jdt23/powermeter/powermeterCommon/powerMeter_case_prototypes - 1.png

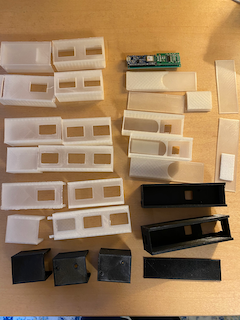
powermeterCommon/powerMeter_case_prototypes - 1.png
