jdt23/powermeter/powermeterSensor/case/powermeterSensor_prototype3_bottom.stl

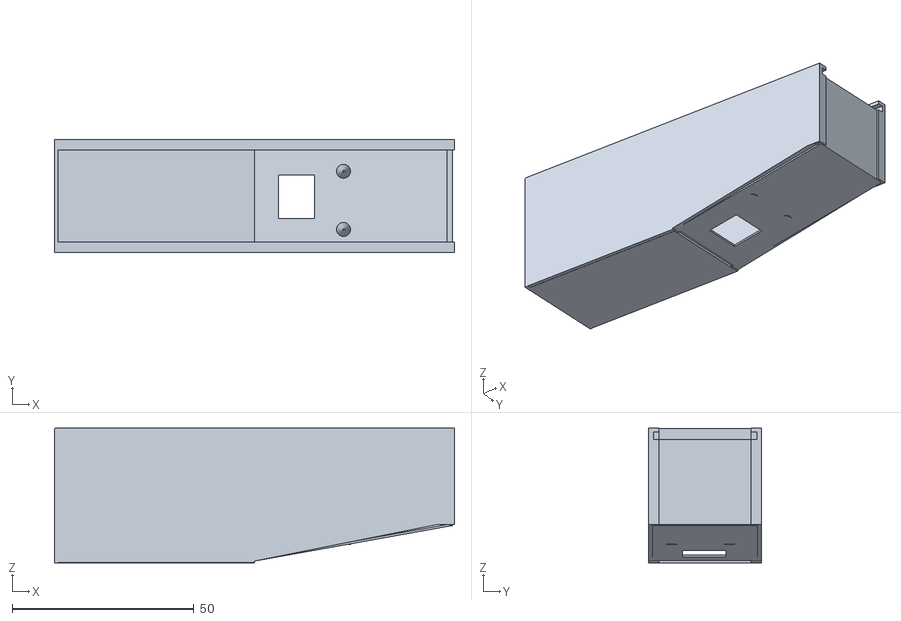
[picture p33: CAD file, 2020-11-20, an earlier design]
powermeterSensor/case/powermeterSensor_prototype3_bottom.stl
110.1 x 31.2 x 37.1
