jdt23/powermeter/powermeterSensor/case/powermeterSensor_prototype3_top.stl

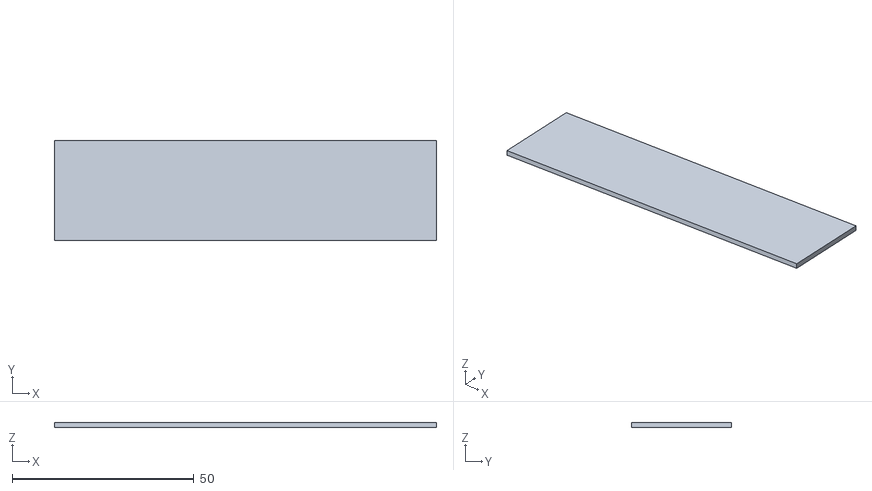
[picture p34: CAD file, 2020-11-20, an earlier design]
powermeterSensor/case/powermeterSensor_prototype3_top.stl
105.0 x 27.5 x 1.50
