jdt23/powermeter/powermeterSensor/case/powermeterSensor_prototype2_bottom.stl

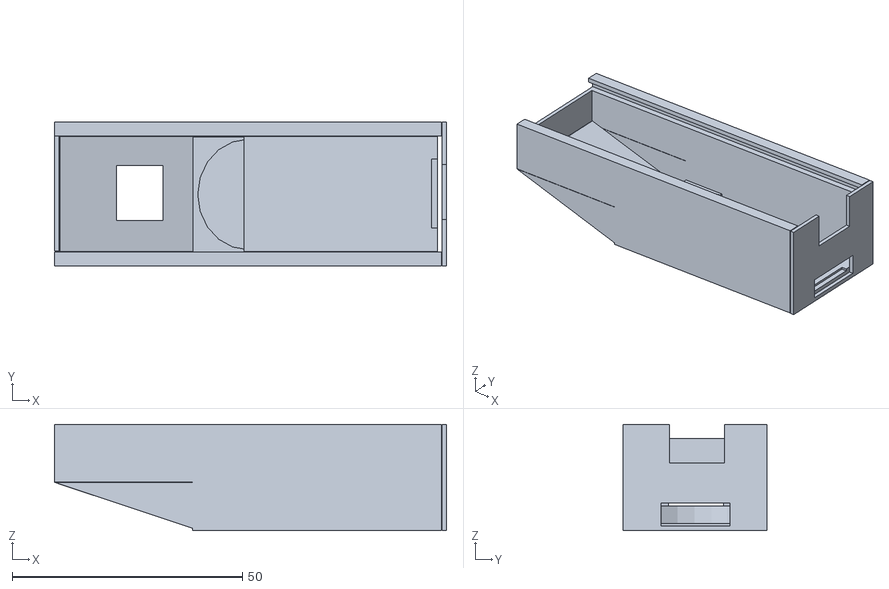
[picture p35: CAD file, 2020-08-12, an earlier design]
powermeterSensor/case/powermeterSensor_prototype2_bottom.stl
85.1 x 31.2 x 23.1
