jdt23/powermeter/powermeterSensor/case/powermeterSensor_prototype1_top.stl

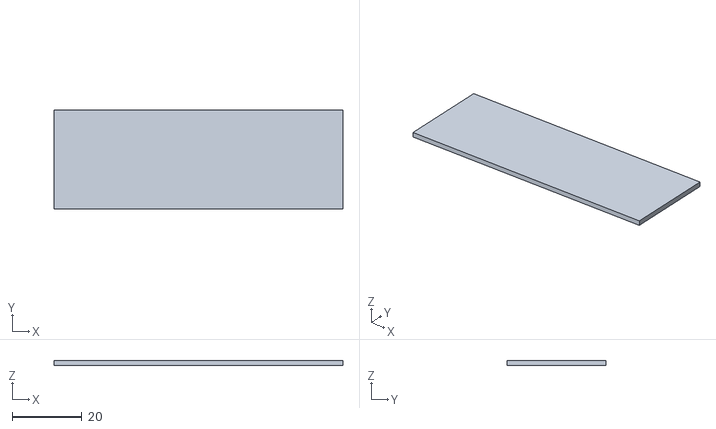
[picture p36: CAD file, 2020-08-12, an earlier design]
powermeterSensor/case/powermeterSensor_prototype1_top.stl
83.0 x 28.5 x 1.50
